Acliad/Ampeater/Ampeater Sim/control_loop_ac.asc

C1: cap; {Chf}; Rser=0.01
C2: cap; {Cff}
C3: cap; {Ccomp}
C4: cap; 1kF
C5: cap; {Chf}; Rser=0.01
C6: cap; {Cff}
C7: cap; {Ccomp}
C8: cap; 1kF
L1: ind; {Lin}; Rser=0.05
L2: ind; 1GH
L3: ind; 10nH; Rser=0.05
L4: ind; 1GH
R1: res; 0.1
R2: res; 4.7k
R3: res; 0.1
R4: res; {Rcomp}
R5: res; {Rff}
R6: res; {Rff}
R7: res; {Rgs}
R8: res; 47
R9: res; {Rgs}
R10: res; 4.7k
R11: res; {Rcomp}
R12: res; 0.01
R13: res; 47
U1: opamp2; TLV9162
U2: IRF3205
U4: opamp2; TLV9162
U7: IRF3205
V2: voltage; 9
V3: voltage; 5
V4: voltage; ""; AC 1
V5: voltage; 1
V6: voltage; 0
V9: voltage; 1
Named nets: Vcc, 0, Vsup, Vout1, Vee, Vbreak_in1, Vbreak_out, Vg2, Vbreak_in2, Vout2, Vo1, Vo2
.tran 0 60us 5u
.lib TLV9162.lib
.lib SC5200.lib
.ac dec 50 1000 100MEG
.lib IRF3205.lib
.lib LMC660.lib
.ic V(Vbreak_in1)=1 V(Vg1)=5.245 V(Vout1)=1 V(Vo1)=5.25 V(Vbreak_in2)=1 V(Vg2)=5.245 V(Vout2)=1 V(Vo1)=5.25
.param Chf=82pF Cff=280pF Rff=100 Rcomp=1.5k Ccomp=470pF Rg=91 Rfb=5.1k Rgs=10k Rhf=1MEG
.step param Rgs list 100 1000 10000
.param Lin=100nH Rin=1.8 Cin=1.0uF
