Acliad/Ampeater/Ampeater Sim/control_loop_transient.asc

C1: cap; {Chf}; Rser=0.01
C2: cap; {Cff}
C3: cap; {Ccomp}
C4: cap; {Cin}
C5: cap; {Chf}; Rser=0.01
C6: cap; {Cff}
C7: cap; {Ccomp}
L1: ind; {Lin}; Rser=0.05
L2: ind; 4.5nH
L3: ind; 7.5nH
L4: ind; 4.5nH
L5: ind; 7.5nH
R1: res; {Rs}
R2: res; {Rfb}
R3: res; {Rcomp}
R4: res; {Rg}
R5: res; {Rff}
R6: res; {Rin}
R7: res; .01
R8: res; {Rs}
R9: res; {Rfb}
R10: res; {Rcomp}
R11: res; {Rg}
R12: res; {Rff}
R13: res; {Rgs}
R14: res; {Rgs}
U1: opamp2; TLV9162
U2: IRF3205
U4: opamp2; TLV9162
U5: IRF3205
V1: voltage; PULSE(0 1 .02m 100p 100p 1 1); Rser=0.01
V2: voltage; 12
V3: voltage; 5
V4: voltage; 1
V5: voltage; 0
Named nets: Vcc, 0, Vsup, Vee, Vg1, V_feedback1, Vref
.tran 0 30us 15u
.lib TLV9162.lib
.lib SC5200.lib
.ac dec 50 100 10MEG
.lib IRF3205.lib
.nodeset V(vout)=1 V(Vg)=5.2 V(V_feedback)=1
.param Chf=82pF Cff=280pF Rff=100 Rcomp=1.5k Ccomp=470pF Rg=91 Rfb=5.1k Rgs=10k Rhf=1MEG
.step param Ccomp 100pF 500pF 100pF
.step dec param Lin 10n 10u 2
.param Lin=100nH Rin=1.8 Cin=1.0uF
.param Rs=0.2
