Acliad/Ampeater/Ampeater Sim/Draft1.asc

C1: cap; 0.1µF
C2: cap; 0.1µF
L1: ind; 15mH
L2: ind; 15mH
R1: res; 1.5k
R2: res; 1.5k
R3: res; 28
V1: voltage; ""; AC 1
V2: voltage; ""; AC 1
Named nets: 0
.ac dec 100 100 100k
Inductor series resistance
Ideal
Non-ideal
