Acliad/Ampeater/Software/Core/Src/adc.c

/**
  ******************************************************************************
  * @file    adc.c
  * @brief   This file provides code for the configuration
  *          of the ADC instances.
  ******************************************************************************
  * @attention
  *
  * <h2><center>&copy; Copyright (c) 2022 STMicroelectronics.
  * All rights reserved.</center></h2>
  *
  * This software component is licensed by ST under BSD 3-Clause license,
  * the "License"; You may not use this file except in compliance with the
  * License. You may obtain a copy of the License at:
  *                        opensource.org/licenses/BSD-3-Clause
  *
  ******************************************************************************
  */

/* Includes ------------------------------------------------------------------*/
#include "adc.h"

/* USER CODE BEGIN 0 */
uint16_t adc_buffer[ADC_NUM_CHANNELS] = {0};
#define ADC_BUF_LEN_BYTES ADC_NUM_CHANNELS*sizeof(adc_buffer[0])
/* USER CODE END 0 */

ADC_HandleTypeDef hadc;
DMA_HandleTypeDef hdma_adc;

/* ADC init function */
void MX_ADC_Init(void)
{
  ADC_ChannelConfTypeDef sConfig = {0};

  /** Configure the global features of the ADC (Clock, Resolution, Data Alignment and number of conversion)
  */
  hadc.Instance = ADC1;
  hadc.Init.OversamplingMode = DISABLE;
  hadc.Init.ClockPrescaler = ADC_CLOCK_SYNC_PCLK_DIV1;
  hadc.Init.Resolution = ADC_RESOLUTION_12B;
  hadc.Init.SamplingTime = ADC_SAMPLETIME_160CYCLES_5;
  hadc.Init.ScanConvMode = ADC_SCAN_DIRECTION_FORWARD;
  hadc.Init.DataAlign = ADC_DATAALIGN_RIGHT;
  hadc.Init.ContinuousConvMode = DISABLE;
  hadc.Init.DiscontinuousConvMode = DISABLE;
  hadc.Init.ExternalTrigConvEdge = ADC_EXTERNALTRIGCONVEDGE_NONE;
  hadc.Init.ExternalTrigConv = ADC_SOFTWARE_START;
  hadc.Init.DMAContinuousRequests = DISABLE;
  hadc.Init.EOCSelection = ADC_EOC_SEQ_CONV;
  hadc.Init.Overrun = ADC_OVR_DATA_PRESERVED;
  hadc.Init.LowPowerAutoWait = DISABLE;
  hadc.Init.LowPowerFrequencyMode = DISABLE;
  hadc.Init.LowPowerAutoPowerOff = DISABLE;
  if (HAL_ADC_Init(&hadc) != HAL_OK)
  {
    Error_Handler();
  }
  /** Configure for the selected ADC regular channel to be converted.
  */
  sConfig.Channel = ADC_CHANNEL_0;
  sConfig.Rank = ADC_RANK_CHANNEL_NUMBER;
  if (HAL_ADC_ConfigChannel(&hadc, &sConfig) != HAL_OK)
  {
    Error_Handler();
  }
  /** Configure for the selected ADC regular channel to be converted.
  */
  sConfig.Channel = ADC_CHANNEL_1;
  if (HAL_ADC_ConfigChannel(&hadc, &sConfig) != HAL_OK)
  {
    Error_Handler();
  }
  /** Configure for the selected ADC regular channel to be converted.
  */
  sConfig.Channel = ADC_CHANNEL_9;
  if (HAL_ADC_ConfigChannel(&hadc, &sConfig) != HAL_OK)
  {
    Error_Handler();
  }

}

void HAL_ADC_MspInit(ADC_HandleTypeDef* adcHandle)
{

  GPIO_InitTypeDef GPIO_InitStruct = {0};
  if(adcHandle->Instance==ADC1)
  {
    /* ADC1 clock enable */
    __HAL_RCC_ADC1_CLK_ENABLE();

    __HAL_RCC_GPIOA_CLK_ENABLE();
    __HAL_RCC_GPIOB_CLK_ENABLE();
    /**ADC GPIO Configuration
    PA0-CK_IN     ------> ADC_IN0
    PA1     ------> ADC_IN1
    PB1     ------> ADC_IN9
    */
    GPIO_InitStruct.Pin = Vsense_R_Pin|Vsense_FET_Pin;
    GPIO_InitStruct.Mode = GPIO_MODE_ANALOG;
    GPIO_InitStruct.Pull = GPIO_NOPULL;
    HAL_GPIO_Init(GPIOA, &GPIO_InitStruct);

    GPIO_InitStruct.Pin = Vbtns_Pin;
    GPIO_InitStruct.Mode = GPIO_MODE_ANALOG;
    GPIO_InitStruct.Pull = GPIO_NOPULL;
    HAL_GPIO_Init(Vbtns_GPIO_Port, &GPIO_InitStruct);

    /* ADC1 DMA Init */
    /* ADC Init */
    hdma_adc.Instance = DMA1_Channel1;
    hdma_adc.Init.Request = DMA_REQUEST_0;
    hdma_adc.Init.Direction = DMA_PERIPH_TO_MEMORY;
    hdma_adc.Init.PeriphInc = DMA_PINC_DISABLE;
    hdma_adc.Init.MemInc = DMA_MINC_ENABLE;
    hdma_adc.Init.PeriphDataAlignment = DMA_PDATAALIGN_HALFWORD;
    hdma_adc.Init.MemDataAlignment = DMA_MDATAALIGN_HALFWORD;
    hdma_adc.Init.Mode = DMA_NORMAL;
    hdma_adc.Init.Priority = DMA_PRIORITY_LOW;
    if (HAL_DMA_Init(&hdma_adc) != HAL_OK)
    {
      Error_Handler();
    }

    __HAL_LINKDMA(adcHandle,DMA_Handle,hdma_adc);

  }
}

void HAL_ADC_MspDeInit(ADC_HandleTypeDef* adcHandle)
{

  if(adcHandle->Instance==ADC1)
  {
    /* Peripheral clock disable */
    __HAL_RCC_ADC1_CLK_DISABLE();

    /**ADC GPIO Configuration
    PA0-CK_IN     ------> ADC_IN0
    PA1     ------> ADC_IN1
    PB1     ------> ADC_IN9
    */
    HAL_GPIO_DeInit(GPIOA, Vsense_R_Pin|Vsense_FET_Pin);

    HAL_GPIO_DeInit(Vbtns_GPIO_Port, Vbtns_Pin);

    /* ADC1 DMA DeInit */
    HAL_DMA_DeInit(adcHandle->DMA_Handle);
  }
}

/* USER CODE BEGIN 1 */
ADC_HandleTypeDef *HAL_ADC_getInstance(void) { 
    return &hadc; 
  }


uint16_t ADC_readChannel(uint32_t channel_idx) {
  if (channel_idx >= ADC_NUM_CHANNELS) {
    Error_Handler();
  }
  HAL_ADC_Start_DMA(&hadc, (uint32_t*)adc_buffer, ADC_BUF_LEN_BYTES);
  HAL_ADC_PollForConversion(&hadc, HAL_MAX_DELAY);
  HAL_ADC_Stop_DMA(&hadc);

  return adc_buffer[channel_idx];
}
/* USER CODE END 1 */

/************************ (C) COPYRIGHT STMicroelectronics *****END OF FILE****/
