Acliad/Ampeater/Software/Core/Src/gpio.c

/**
  ******************************************************************************
  * @file    gpio.c
  * @brief   This file provides code for the configuration
  *          of all used GPIO pins.
  ******************************************************************************
  * @attention
  *
  * <h2><center>&copy; Copyright (c) 2022 STMicroelectronics.
  * All rights reserved.</center></h2>
  *
  * This software component is licensed by ST under BSD 3-Clause license,
  * the "License"; You may not use this file except in compliance with the
  * License. You may obtain a copy of the License at:
  *                        opensource.org/licenses/BSD-3-Clause
  *
  ******************************************************************************
  */

/* Includes ------------------------------------------------------------------*/
#include "gpio.h"

/*----------------------------------------------------------------------------*/
/* Configure GPIO                                                             */
/*----------------------------------------------------------------------------*/
/** Configure pins as
        * Analog
        * Input
        * Output
        * EVENT_OUT
        * EXTI
*/
void MX_GPIO_Init(void)
{

  GPIO_InitTypeDef GPIO_InitStruct = {0};

  /* GPIO Ports Clock Enable */
  __HAL_RCC_GPIOC_CLK_ENABLE();
  __HAL_RCC_GPIOA_CLK_ENABLE();
  __HAL_RCC_GPIOB_CLK_ENABLE();

  /*Configure GPIO pin Output Level */
  HAL_GPIO_WritePin(GPIOA, SPI_CS_DAC_Pin|SPI_nRST_LCD_Pin|RANGE_SW_Pin, GPIO_PIN_RESET);

  /*Configure GPIO pin : PtPin */
  GPIO_InitStruct.Pin = ENCODER_A_Pin;
  GPIO_InitStruct.Mode = GPIO_MODE_IT_RISING_FALLING;
  GPIO_InitStruct.Pull = GPIO_PULLUP;
  HAL_GPIO_Init(ENCODER_A_GPIO_Port, &GPIO_InitStruct);

  /*Configure GPIO pin : PtPin */
  GPIO_InitStruct.Pin = ENCODER_B_Pin;
  GPIO_InitStruct.Mode = GPIO_MODE_IT_RISING;
  GPIO_InitStruct.Pull = GPIO_PULLUP;
  HAL_GPIO_Init(ENCODER_B_GPIO_Port, &GPIO_InitStruct);

  /*Configure GPIO pins : PAPin PAPin */
  GPIO_InitStruct.Pin = SPI_CS_DAC_Pin|SPI_nRST_LCD_Pin;
  GPIO_InitStruct.Mode = GPIO_MODE_OUTPUT_PP;
  GPIO_InitStruct.Pull = GPIO_NOPULL;
  GPIO_InitStruct.Speed = GPIO_SPEED_FREQ_VERY_HIGH;
  HAL_GPIO_Init(GPIOA, &GPIO_InitStruct);

  /*Configure GPIO pin : PtPin */
  GPIO_InitStruct.Pin = RANGE_SW_Pin;
  GPIO_InitStruct.Mode = GPIO_MODE_OUTPUT_PP;
  GPIO_InitStruct.Pull = GPIO_NOPULL;
  GPIO_InitStruct.Speed = GPIO_SPEED_FREQ_LOW;
  HAL_GPIO_Init(RANGE_SW_GPIO_Port, &GPIO_InitStruct);

  /* EXTI interrupt init*/
  HAL_NVIC_SetPriority(EXTI4_15_IRQn, 0, 0);
  HAL_NVIC_EnableIRQ(EXTI4_15_IRQn);

}

/* USER CODE BEGIN 2 */
void GPIO_InitLCD(void) {
  GPIO_InitTypeDef GPIO_InitStruct = {0};

  __HAL_RCC_GPIOA_CLK_ENABLE();

  /*Configure GPIO pin Output Level */
  HAL_GPIO_WritePin(UART_TX_SPI_CS_LCD_GPIO_Port, 
                    UART_TX_SPI_CS_LCD_Pin, 
                    GPIO_PIN_RESET);
  HAL_GPIO_WritePin(UART_RX_SPI_DC_LCD_GPIO_Port, 
                    UART_RX_SPI_DC_LCD_Pin, 
                    GPIO_PIN_RESET);
  HAL_GPIO_WritePin(SPI_nRST_LCD_GPIO_Port, 
                    SPI_nRST_LCD_Pin, 
                    GPIO_PIN_RESET);

  GPIO_InitStruct.Pin = UART_TX_SPI_CS_LCD_Pin;
  GPIO_InitStruct.Mode = GPIO_MODE_OUTPUT_PP;
  GPIO_InitStruct.Pull = GPIO_NOPULL;
  GPIO_InitStruct.Speed = GPIO_SPEED_FREQ_VERY_HIGH;
  HAL_GPIO_Init(UART_TX_SPI_CS_LCD_GPIO_Port, &GPIO_InitStruct);     

  GPIO_InitStruct.Pin = UART_RX_SPI_DC_LCD_Pin;    
  HAL_GPIO_Init(UART_RX_SPI_DC_LCD_GPIO_Port, &GPIO_InitStruct);        

  GPIO_InitStruct.Pin = SPI_nRST_LCD_Pin;    
  HAL_GPIO_Init(SPI_nRST_LCD_GPIO_Port, &GPIO_InitStruct);        
}
/* USER CODE END 2 */

/************************ (C) COPYRIGHT STMicroelectronics *****END OF FILE****/
