Acliad/Ampeater/Software/Core/Src/usart.c

/**
  ******************************************************************************
  * @file    usart.c
  * @brief   This file provides code for the configuration
  *          of the USART instances.
  ******************************************************************************
  * @attention
  *
  * <h2><center>&copy; Copyright (c) 2022 STMicroelectronics.
  * All rights reserved.</center></h2>
  *
  * This software component is licensed by ST under BSD 3-Clause license,
  * the "License"; You may not use this file except in compliance with the
  * License. You may obtain a copy of the License at:
  *                        opensource.org/licenses/BSD-3-Clause
  *
  ******************************************************************************
  */

/* Includes ------------------------------------------------------------------*/
#include "usart.h"

/* USER CODE BEGIN 0 */
#include <string.h>
/* USER CODE END 0 */

UART_HandleTypeDef huart2;

/* USART2 init function */

void MX_USART2_UART_Init(void)
{

  huart2.Instance = USART2;
  huart2.Init.BaudRate = 115200;
  huart2.Init.WordLength = UART_WORDLENGTH_8B;
  huart2.Init.StopBits = UART_STOPBITS_1;
  huart2.Init.Parity = UART_PARITY_NONE;
  huart2.Init.Mode = UART_MODE_TX_RX;
  huart2.Init.HwFlowCtl = UART_HWCONTROL_NONE;
  huart2.Init.OverSampling = UART_OVERSAMPLING_16;
  huart2.Init.OneBitSampling = UART_ONE_BIT_SAMPLE_DISABLE;
  huart2.AdvancedInit.AdvFeatureInit = UART_ADVFEATURE_NO_INIT;
  if (HAL_UART_Init(&huart2) != HAL_OK)
  {
    Error_Handler();
  }

}

void HAL_UART_MspInit(UART_HandleTypeDef* uartHandle)
{

  GPIO_InitTypeDef GPIO_InitStruct = {0};
  if(uartHandle->Instance==USART2)
  {
    /* USART2 clock enable */
    __HAL_RCC_USART2_CLK_ENABLE();

    __HAL_RCC_GPIOA_CLK_ENABLE();
    /**USART2 GPIO Configuration
    PA2     ------> USART2_TX
    PA3     ------> USART2_RX
    */
    GPIO_InitStruct.Pin = UART_TX_SPI_CS_LCD_Pin|UART_RX_SPI_DC_LCD_Pin;
    GPIO_InitStruct.Mode = GPIO_MODE_AF_PP;
    GPIO_InitStruct.Pull = GPIO_NOPULL;
    GPIO_InitStruct.Speed = GPIO_SPEED_FREQ_VERY_HIGH;
    GPIO_InitStruct.Alternate = GPIO_AF4_USART2;
    HAL_GPIO_Init(GPIOA, &GPIO_InitStruct);

  }
}

void HAL_UART_MspDeInit(UART_HandleTypeDef* uartHandle)
{

  if(uartHandle->Instance==USART2)
  {
    /* Peripheral clock disable */
    __HAL_RCC_USART2_CLK_DISABLE();

    /**USART2 GPIO Configuration
    PA2     ------> USART2_TX
    PA3     ------> USART2_RX
    */
    HAL_GPIO_DeInit(GPIOA, UART_TX_SPI_CS_LCD_Pin|UART_RX_SPI_DC_LCD_Pin);

  }
}

/* USER CODE BEGIN 1 */
UART_HandleTypeDef* UART_getInstance(uint16_t instance_num)
{
  switch (instance_num)
  {
  case UART2:
    return &huart2;
    break;
  
  default:
    return NULL;
    break;
  }
}

void UART_print(char *out_buff) {
    #ifndef USE_LCD
    HAL_UART_Transmit(&huart2, (uint8_t *)out_buff, strlen(out_buff), 0xFFFF);
    #else
    UNUSED(out_buff)
    #endif
}
/* USER CODE END 1 */

/************************ (C) COPYRIGHT STMicroelectronics *****END OF FILE****/
